RTimothyEdwards/chipalooza_projects_1/netlist/schematic/chipalooza_testchip1.spice

** sch_path: /home/tim/gits/chipalooza_projects_1/xschem/chipalooza_testchip1.sch
.subckt chipalooza_testchip1 vccd2 vdda1 vdda2 vssa1 la_data_out[37] vssa2 la_data_out[65] la_data_out[36] la_data_out[62]
+ la_data_out[64] la_data_out[63] gpio_noesd[7] io_analog[4] gpio_analog[8] la_data_out[67] la_data_out[60] la_data_out[66] la_data_out[61]
+ io_out[13] la_data_out[34] io_analog[10] la_data_out[124] gpio_analog[9] la_data_out[91] la_data_out[69] la_data_out[58] la_data_out[87]
+ la_data_out[68] la_data_out[35] gpio_analog[6] ls_data_out[59] la_data_out[88] la_data_out[89] io_analog[3] la_data_out[90] la_data_out[17]
+ io_analog[9] la_data_out[123] gpio_analog[10] la_data_out[71] la_data_out[56] gpio_analog[5] la_data_out[70] la_data_out[57] io_analog[8]
+ la_data_out[25] la_data_out[73] la_data_out[54] la_data_out[26] io_out[17] la_data_out[72] la_data_out[55] la_data_out[27] la_data_out[86]
+ la_data_out[29] la_data_out[33] io_out[12] la_data_out[30] la_data_out[28] la_data_out[32] la_data_out[85] io_analog[2] io_analog[7]
+ la_data_out[31] la_data_out[122] la_data_out[75] la_data_out[52] la_data_out[74] la_data_out[53] gpio_noesd[2] gpio_noesd[3] gpio_noesd[4]
+ la_data_out[23] io_analog[1] io_analog[6] gpio_analog[11] la_data_out[121] la_data_out[77] la_data_out[50] la_data_out[76] gpio_analog[1]
+ la_data_out[51] io_out[8] la_data_out[22] io_out[7] la_data_out[96] io_analog[0] io_out[3] io_analog[5] la_data_out[97] io_out[2] gpio_analog[13]
+ la_data_out[98] gpio_analog[12] io_out[4] la_data_out[94] la_data_out[118] la_data_out[93] la_data_in[120] la_data_out[92] la_data_out[99]
+ la_data_in[119] gpio_analog[0] la_data_out[95] la_data_out[21] io_out[6] la_data_out[105] gpio_analog[17] la_data_out[104] la_data_out[48]
+ la_data_out[103] la_data_out[41] la_data_out[102] la_data_out[44] la_data_out[100] la_data_out[40] la_data_out[101] la_data_out[42]
+ la_data_out[38] la_data_out[46] la_data_out[19] la_data_out[47] la_data_out[20] la_data_out[49] io_out[23] la_data_out[45] gpio_analog[15]
+ gpio_analog[14] la_data_out[39] la_data_out[43] la_data_out[78] la_data_out[125] io_out[0] la_data_out[84] la_data_out[82] io_out[1]
+ la_data_out[81] la_data_out[112] la_data_out[16] la_data_out[83] la_data_out[113] la_data_out[15] la_data_out[80] la_data_out[111]
+ la_data_out[14] la_data_out[79] la_data_out[13] la_data_out[107] la_data_out[109] la_data_in[117] la_data_out[12] la_data_out[106]
+ la_data_out[115] io_out[5] la_data_out[11] la_data_out[108] la_data_out[114] la_data_out[10] la_data_out[116] la_data_out[9] la_data_out[110]
+ la_data_out[8] la_data_out[7] la_data_out[6] la_data_out[5] la_data_out[4] la_data_out[3] la_data_out[2] la_data_out[1] gpio_analog[18]
+ io_oeb[0] io_oeb[17] io_oeb[1] io_oeb[23] io_oeb[2] io_oeb[3] io_oeb[4] io_oeb[5] io_oeb[6] io_oeb[7] io_oeb[8] io_oeb[12] io_oeb[13]
*.PININFO vdda1:I vssa1:I vccd2:I vdda2:I vssa2:I la_data_out[50]:I la_data_out[51]:I la_data_out[62]:I la_data_out[63]:I
*+ la_data_out[60]:I la_data_out[61]:I la_data_out[58]:I ls_data_out[59]:I la_data_out[56]:I la_data_out[57]:I la_data_out[54]:I la_data_out[55]:I
*+ la_data_out[52]:I la_data_out[53]:I la_data_out[77]:I la_data_out[76]:I la_data_out[75]:I la_data_out[74]:I la_data_out[73]:I la_data_out[72]:I
*+ la_data_out[71]:I la_data_out[70]:I la_data_out[69]:I la_data_out[68]:I la_data_out[67]:I la_data_out[66]:I la_data_out[65]:I la_data_out[64]:I
*+ gpio_analog[17]:I la_data_out[49]:I la_data_out[48]:I la_data_out[47]:I la_data_out[46]:I la_data_out[45]:I la_data_out[44]:I la_data_out[43]:I
*+ la_data_out[42]:I la_data_out[41]:I la_data_out[40]:I la_data_out[39]:I la_data_out[38]:I la_data_out[84]:I la_data_out[83]:I la_data_out[82]:I
*+ la_data_out[81]:I la_data_out[80]:I la_data_out[79]:I la_data_out[78]:I la_data_out[125]:I vssa1:I vdda1:I gpio_analog[18]:B gpio_analog[14]:B
*+ gpio_analog[15]:B la_data_out[19]:I la_data_out[20]:I io_out[23]:O la_data_out[16]:I gpio_analog[13]:B la_data_out[21]:I gpio_analog[12]:B
*+ gpio_analog[11]:B la_data_out[22]:I la_data_out[23]:I la_data_out[33]:I la_data_out[32]:I la_data_out[31]:I la_data_out[27]:I la_data_out[26]:I
*+ la_data_out[25]:I io_out[17]:O la_data_out[30]:I la_data_out[29]:I la_data_out[28]:I gpio_analog[10]:B la_data_out[17]:I la_data_out[34]:I
*+ la_data_out[36]:I gpio_analog[9]:B gpio_analog[8]:B la_data_out[35]:I la_data_out[37]:I gpio_noesd[7]:B io_out[13]:O la_data_out[91]:I
*+ la_data_out[90]:I la_data_out[89]:I la_data_out[88]:I la_data_out[87]:I gpio_analog[6]:B la_data_out[124]:I gpio_analog[5]:B la_data_out[123]:I
*+ io_out[12]:O gpio_noesd[4]:B gpio_noesd[3]:B la_data_out[85]:I la_data_out[86]:I gpio_noesd[2]:B la_data_out[122]:I gpio_analog[1]:B
*+ la_data_out[121]:I gpio_analog[0]:B la_data_out[118]:I io_out[2]:O io_out[7]:O io_out[8]:O io_out[3]:O la_data_in[119]:O la_data_out[92]:I
*+ la_data_out[93]:I la_data_out[94]:I io_out[4]:O la_data_out[98]:I la_data_out[97]:I la_data_out[96]:I la_data_out[95]:I la_data_out[99]:I
*+ la_data_in[120]:O io_out[6]:O la_data_out[105]:I la_data_out[104]:I la_data_out[103]:I la_data_out[102]:I la_data_out[101]:I la_data_out[100]:I
*+ io_out[0]:O io_out[5]:O la_data_out[107]:I la_data_out[106]:I la_data_out[108]:I la_data_in[117]:O la_data_out[116]:I io_out[1]:O
*+ la_data_out[115]:I la_data_out[114]:I la_data_out[112]:I la_data_out[113]:I la_data_out[111]:I la_data_out[110]:I la_data_out[109]:I io_oeb[0]:O
*+ io_oeb[1]:O io_oeb[2]:O io_oeb[3]:O io_oeb[4]:O io_oeb[5]:O io_oeb[6]:O io_oeb[7]:O io_oeb[8]:O io_oeb[12]:O io_oeb[13]:O io_oeb[17]:O
*+ io_oeb[23]:O io_analog[10]:B io_analog[9]:B io_analog[8]:B io_analog[7]:B io_analog[6]:B io_analog[5]:B io_analog[0]:B io_analog[1]:B
*+ io_analog[2]:B io_analog[3]:B io_analog[4]:B la_data_out[1]:I la_data_out[2]:I la_data_out[3]:I la_data_out[4]:I la_data_out[5]:I
*+ la_data_out[6]:I la_data_out[7]:I la_data_out[8]:I la_data_out[9]:I la_data_out[10]:I la_data_out[11]:I la_data_out[12]:I la_data_out[13]:I
*+ la_data_out[14]:I la_data_out[15]:I la_data_out[16]:I
x1 vdda1 gpio_analog[17] la_data_out[48] la_data_out[41] la_data_out[44] la_data_out[40] la_data_out[42] la_data_out[38]
+ la_data_out[46] la_data_out[47] la_data_out[49] la_data_out[45] la_data_out[39] la_data_out[43] src_200_0 src_10000_0 src_400 src_600 src_test1
+ src_200_1 src_100 src_10000_1 src_50 src_test0 src_200_2 la_data_out[78] la_data_out[125] la_data_out[84] la_data_out[82] la_data_out[81]
+ la_data_out[83] la_data_out[80] ibias_nc3 ibias_nc1 snk_5000_1 snk_test1 snk_3700 ibias_nc2 snk_test0 la_data_out[79] vssa1 bias_generator
x2 la_data_out[62] la_data_out[63] vssa2 vdda2 vdd_spare_3 power_stage
x3 la_data_out[60] la_data_out[61] vssa2 vdda2 io_analog[10] power_stage
x4 la_data_out[58] ls_data_out[59] vssa2 vccd2 io_analog[9] power_stage
x5 la_data_out[56] la_data_out[57] vssa2 vdda2 io_analog[8] power_stage
x6 la_data_out[54] la_data_out[55] vssa2 vdda2 io_analog[7] power_stage
x7 la_data_out[52] la_data_out[53] vssa2 vdda2 io_analog[6] power_stage
x8 la_data_out[50] la_data_out[51] vssa2 vccd2 io_analog[5] power_stage
x9 la_data_out[65] la_data_out[64] vssa1 vdda1 io_analog[4] power_stage
x10 la_data_out[67] la_data_out[66] vssa1 vdda1 vdd_spare_2 power_stage
x11 la_data_out[69] la_data_out[68] vssa1 vdda1 io_analog[3] power_stage
x12 la_data_out[71] la_data_out[70] vssa1 vdda1 vdd_spare_1 power_stage
x13 la_data_out[73] la_data_out[72] vssa1 vdda1 io_analog[2] power_stage
x14 la_data_out[75] la_data_out[74] vssa1 vdda1 io_analog[1] power_stage
x15 la_data_out[77] la_data_out[76] vssa1 vdda1 io_analog[0] power_stage
X17 net4 gpio_analog[13] src_10000_1 net20 vssa2 io_analog[7] net2 net1 net3 lpopamp
x18 io_analog[0] vssa1 io_out[0] vccd1 net21 vssd1 io_out[1] vbgA net15 net15 net15 net22 net23 net16 net16 net16 net24
+ la_data_out[109] la_data_out[115] net25 la_data_out[114] la_data_in[117] io_out[5] la_data_out[116] la_data_out[110] src_200_0
+ sky130_ajc_ip__brownout
x19 io_analog[1] vssa1 vccd1 vssd1 vbgA io_out[6] net26 net14 net14 net14 net14 net27 la_data_out[100] la_data_out[101] src_200_1
+ sky130_ajc_ip__overvoltage
x20 io_analog[2] net28 io_out[8] vssa1 vccd1 io_out[7] vssd1 io_out[3] vbgA io_out[2] net13 net13 net13 net29 la_data_out[94]
+ io_out[4] net30 la_data_out[93] la_data_out[92] la_data_in[120] la_data_in[119] la_data_out[99] la_data_out[95] src_200_2
+ sky130_ajc_ip__por
x21 vccd2 io_analog[8] vssa2 net6 io_out[17] net5 la_data_out[28] net8 net8 net7 net7 net7 net7 net7 net7 src_400
+ sky130_ak_ip__comparator
x22 io_analog[3] vssa1 vccd1 vssd1 src_50 la_data_out[86] la_data_out[85] io_out[12] gpio_noesd[3] gpio_noesd[4]
+ sky130_be_ip__lsxo
X23 gpio_analog[15] gpio_analog[14] la_data_out[19] la_data_out[20] io_out[23] io_analog[6] vccd2 vssa2 vssd2 src_10000_0 vssd2
+ sky130_ht_ip__hsxo_cpz1
x25 io_analog[10] gpio_noesd[7] src_100 net12 net11 vssa2 vccd2 vssd2 la_data_out[37] sky130_td_ip__opamp_hp
x26 io_analog[4] vccd1 la_data_out[91] la_data_out[87] src_600 la_data_out[88] io_out[13] vbgA la_data_out[89] la_data_out[90]
+ vssd1 vssa1 sky130_vbl_ip__overvoltage
x28 la_data_out[21] net1 net2 vccd2 vssd2 avdd2 lvl_shift_invert
x29 avss2 la_data_out[22] net5 avdd2 net3 gpio_analog[12] vccd2 vssd2 analog_mux_sel1v8
x30 avss2 la_data_out[23] net6 avdd2 net4 gpio_analog[11] vccd2 vssd2 analog_mux_sel1v8
x31 vccd2 vssd2 vssa2 la_data_out[17] gpio_analog[10] src_test1 avdd2 isolated_switch_ena1v8
x32 net10 io_analog[9] vssd2 vbgA la_data_out[35] net9 sky130_od_ip__tempsensor_ext_vp
x24 avss2 la_data_out[34] net11 avdd2 net9 gpio_analog[9] vccd2 vssd2 analog_mux_sel1v8
x33 avss2 la_data_out[36] net12 avdd2 net10 gpio_analog[8] vccd2 vssd2 analog_mux_sel1v8
x34 vccd1 vssd1 vssa1 la_data_out[124] gpio_analog[6] snk_test1 avdd1 isolated_switch_ena1v8
x35 vccd1 vssd1 vssa1 la_data_out[123] gpio_analog[5] snk_3700 avdd1 isolated_switch_ena1v8
x36 avss1 la_data_out[122] vbgA avdd1 vbgB gpio_noesd[2] vccd1 vssd1 analog_mux_sel1v8
x37 vccd1 vssd1 vssa1 la_data_out[121] gpio_analog[1] snk_5000_1 avdd1 isolated_switch_ena1v8
x38 vccd1 vssd1 vssa1 la_data_out[118] gpio_analog[0] snk_test0 avdd1 isolated_switch_ena1v8
x16 io_analog[5] net19 vssd2 net17 net18 net18 net18 net18 net18 net18 net18 net18 net18 net18 net18 net18 net18 net18 net18 net18
+ bandgap
x39 io_analog[5] vssd2 net31 net17 bias_basis_current
x40 vssa2 la_data_out[16] net19 avdd2 src_test0 gpio_analog[18] vccd2 vssd2 analog_mux_sel1v8
.ends

* expanding   symbol:  bias_generator.sym # of pins=41
** sym_path: /home/tim/gits/chipalooza_projects_1/xschem/bias_generator.sym
** sch_path: /home/tim/gits/chipalooza_projects_1/xschem/bias_generator.sch
.subckt bias_generator avdd ref_in enb enb_200_2 enb_400 enb_100 enb_200_1 enb_test1 enb_10000_1 enb_10000_0 enb_test0 enb_600
+ enb_50 enb_200_0 src_200_0 src_10000_0 src_400 src_600 src_test1 src_200_1 src_100 src_10000_1 src_50 src_test0 src_200_2 ena_test0
+ ena_2000 ena_test1 ena_5000_2 ena_5000_1 ena_3700 ena_5000_0 snk_5000_2 snk_2000 snk_5000_1 snk_test1 snk_3700 snk_5000_0 snk_test0 ena
+ avss
*.PININFO ref_in:I avss:B ena:I enb:I avdd:B enb_test0:I ena_test0:I src_test0:B snk_test0:B ena_test1:I snk_test1:B enb_test1:I
*+ src_test1:B enb_10000_0:I src_10000_0:B ena_5000_0:I snk_5000_0:B enb_10000_1:I src_10000_1:B ena_5000_1:I snk_5000_1:B ena_5000_2:I
*+ snk_5000_2:B enb_600:I src_600:B enb_400:I src_400:B enb_200_0:I src_200_0:B enb_200_1:I src_200_1:B enb_200_2:I src_200_2:B enb_100:I
*+ src_100:B enb_50:I src_50:B ena_3700:I snk_3700:B ena_2000:I snk_2000:B
x2[19] net1 ena nbias nbias avss bias_nstack
x2[18] net1 ena nbias nbias avss bias_nstack
x2[17] net1 ena nbias nbias avss bias_nstack
x2[16] net1 ena nbias nbias avss bias_nstack
x2[15] net1 ena nbias nbias avss bias_nstack
x2[14] net1 ena nbias nbias avss bias_nstack
x2[13] net1 ena nbias nbias avss bias_nstack
x2[12] net1 ena nbias nbias avss bias_nstack
x2[11] net1 ena nbias nbias avss bias_nstack
x2[10] net1 ena nbias nbias avss bias_nstack
x2[9] net1 ena nbias nbias avss bias_nstack
x2[8] net1 ena nbias nbias avss bias_nstack
x2[7] net1 ena nbias nbias avss bias_nstack
x2[6] net1 ena nbias nbias avss bias_nstack
x2[5] net1 ena nbias nbias avss bias_nstack
x2[4] net1 ena nbias nbias avss bias_nstack
x2[3] net1 ena nbias nbias avss bias_nstack
x2[2] net1 ena nbias nbias avss bias_nstack
x2[1] net1 ena nbias nbias avss bias_nstack
x2[0] net1 ena nbias nbias avss bias_nstack
XR3 net1 pcasc avss sky130_fd_pr__res_high_po_0p35 L=900 mult=1 m=1
XR4 pcasc ref_in avss sky130_fd_pr__res_high_po_0p35 L=1500 mult=1 m=1
x4 net2 ena net3 nbias avss bias_nstack
x2 avdd pbias pcasc pbias enb avss net2 bias_pstack
x13[1] avdd pbias pcasc net4[1] enb_test0 avss src_test0 bias_pstack
x13[0] avdd pbias pcasc net4[0] enb_test0 avss src_test0 bias_pstack
x17[1] snk_test0 ena_test0 net5[1] nbias avss bias_nstack
x17[0] snk_test0 ena_test0 net5[0] nbias avss bias_nstack
x18[1] snk_test1 ena_test1 net6[1] nbias avss bias_nstack
x18[0] snk_test1 ena_test1 net6[0] nbias avss bias_nstack
x16[1] avdd pbias pcasc net7[1] enb_test1 avss src_test1 bias_pstack
x16[0] avdd pbias pcasc net7[0] enb_test1 avss src_test1 bias_pstack
x8[199] avdd pbias pcasc net8[199] enb_10000_0 avss src_10000_0 bias_pstack
x8[198] avdd pbias pcasc net8[198] enb_10000_0 avss src_10000_0 bias_pstack
x8[197] avdd pbias pcasc net8[197] enb_10000_0 avss src_10000_0 bias_pstack
x8[196] avdd pbias pcasc net8[196] enb_10000_0 avss src_10000_0 bias_pstack
x8[195] avdd pbias pcasc net8[195] enb_10000_0 avss src_10000_0 bias_pstack
x8[194] avdd pbias pcasc net8[194] enb_10000_0 avss src_10000_0 bias_pstack
x8[193] avdd pbias pcasc net8[193] enb_10000_0 avss src_10000_0 bias_pstack
x8[192] avdd pbias pcasc net8[192] enb_10000_0 avss src_10000_0 bias_pstack
x8[191] avdd pbias pcasc net8[191] enb_10000_0 avss src_10000_0 bias_pstack
x8[190] avdd pbias pcasc net8[190] enb_10000_0 avss src_10000_0 bias_pstack
x8[189] avdd pbias pcasc net8[189] enb_10000_0 avss src_10000_0 bias_pstack
x8[188] avdd pbias pcasc net8[188] enb_10000_0 avss src_10000_0 bias_pstack
x8[187] avdd pbias pcasc net8[187] enb_10000_0 avss src_10000_0 bias_pstack
x8[186] avdd pbias pcasc net8[186] enb_10000_0 avss src_10000_0 bias_pstack
x8[185] avdd pbias pcasc net8[185] enb_10000_0 avss src_10000_0 bias_pstack
x8[184] avdd pbias pcasc net8[184] enb_10000_0 avss src_10000_0 bias_pstack
x8[183] avdd pbias pcasc net8[183] enb_10000_0 avss src_10000_0 bias_pstack
x8[182] avdd pbias pcasc net8[182] enb_10000_0 avss src_10000_0 bias_pstack
x8[181] avdd pbias pcasc net8[181] enb_10000_0 avss src_10000_0 bias_pstack
x8[180] avdd pbias pcasc net8[180] enb_10000_0 avss src_10000_0 bias_pstack
x8[179] avdd pbias pcasc net8[179] enb_10000_0 avss src_10000_0 bias_pstack
x8[178] avdd pbias pcasc net8[178] enb_10000_0 avss src_10000_0 bias_pstack
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
x8[1] avdd pbias pcasc net8[1] enb_10000_0 avss src_10000_0 bias_pstack
x8[0] avdd pbias pcasc net8[0] enb_10000_0 avss src_10000_0 bias_pstack
x9[99] snk_5000_0 ena_5000_0 net9[99] nbias avss bias_nstack
x9[98] snk_5000_0 ena_5000_0 net9[98] nbias avss bias_nstack
x9[97] snk_5000_0 ena_5000_0 net9[97] nbias avss bias_nstack
x9[96] snk_5000_0 ena_5000_0 net9[96] nbias avss bias_nstack
x9[95] snk_5000_0 ena_5000_0 net9[95] nbias avss bias_nstack
x9[94] snk_5000_0 ena_5000_0 net9[94] nbias avss bias_nstack
x9[93] snk_5000_0 ena_5000_0 net9[93] nbias avss bias_nstack
x9[92] snk_5000_0 ena_5000_0 net9[92] nbias avss bias_nstack
x9[91] snk_5000_0 ena_5000_0 net9[91] nbias avss bias_nstack
x9[90] snk_5000_0 ena_5000_0 net9[90] nbias avss bias_nstack
x9[89] snk_5000_0 ena_5000_0 net9[89] nbias avss bias_nstack
x9[88] snk_5000_0 ena_5000_0 net9[88] nbias avss bias_nstack
x9[87] snk_5000_0 ena_5000_0 net9[87] nbias avss bias_nstack
x9[86] snk_5000_0 ena_5000_0 net9[86] nbias avss bias_nstack
x9[85] snk_5000_0 ena_5000_0 net9[85] nbias avss bias_nstack
x9[84] snk_5000_0 ena_5000_0 net9[84] nbias avss bias_nstack
x9[83] snk_5000_0 ena_5000_0 net9[83] nbias avss bias_nstack
x9[82] snk_5000_0 ena_5000_0 net9[82] nbias avss bias_nstack
x9[81] snk_5000_0 ena_5000_0 net9[81] nbias avss bias_nstack
x9[80] snk_5000_0 ena_5000_0 net9[80] nbias avss bias_nstack
x9[79] snk_5000_0 ena_5000_0 net9[79] nbias avss bias_nstack
x9[78] snk_5000_0 ena_5000_0 net9[78] nbias avss bias_nstack
x9[77] snk_5000_0 ena_5000_0 net9[77] nbias avss bias_nstack
x9[76] snk_5000_0 ena_5000_0 net9[76] nbias avss bias_nstack
x9[75] snk_5000_0 ena_5000_0 net9[75] nbias avss bias_nstack
x9[74] snk_5000_0 ena_5000_0 net9[74] nbias avss bias_nstack
x9[73] snk_5000_0 ena_5000_0 net9[73] nbias avss bias_nstack
x9[72] snk_5000_0 ena_5000_0 net9[72] nbias avss bias_nstack
x9[71] snk_5000_0 ena_5000_0 net9[71] nbias avss bias_nstack
x9[70] snk_5000_0 ena_5000_0 net9[70] nbias avss bias_nstack
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
