RTimothyEdwards/chipalooza_projects_1/netlist/schematic/bias_generator.spice

** sch_path: /home/tim/gits/chipalooza_projects_1/xschem/bias_generator.sch
.subckt bias_generator avdd ref_in enb enb_200_2 enb_400 enb_100 enb_200_1 enb_test1 enb_10000_1 enb_10000_0 enb_test0 enb_600
+ enb_50 enb_200_0 src_200_0 src_10000_0 src_400 src_600 src_test1 src_200_1 src_100 src_10000_1 src_50 src_test0 src_200_2 ena_test0
+ ena_2000 ena_test1 ena_5000_2 ena_5000_1 ena_3700 ena_5000_0 snk_5000_2 snk_2000 snk_5000_1 snk_test1 snk_3700 snk_5000_0 snk_test0 ena
+ avss
*.PININFO ref_in:I avss:B ena:I enb:I avdd:B enb_test0:I ena_test0:I src_test0:B snk_test0:B ena_test1:I snk_test1:B enb_test1:I
*+ src_test1:B enb_10000_0:I src_10000_0:B ena_5000_0:I snk_5000_0:B enb_10000_1:I src_10000_1:B ena_5000_1:I snk_5000_1:B ena_5000_2:I
*+ snk_5000_2:B enb_600:I src_600:B enb_400:I src_400:B enb_200_0:I src_200_0:B enb_200_1:I src_200_1:B enb_200_2:I src_200_2:B enb_100:I
*+ src_100:B enb_50:I src_50:B ena_3700:I snk_3700:B ena_2000:I snk_2000:B
x2[19] net1 ena nbias nbias avss bias_nstack
x2[18] net1 ena nbias nbias avss bias_nstack
x2[17] net1 ena nbias nbias avss bias_nstack
x2[16] net1 ena nbias nbias avss bias_nstack
x2[15] net1 ena nbias nbias avss bias_nstack
x2[14] net1 ena nbias nbias avss bias_nstack
x2[13] net1 ena nbias nbias avss bias_nstack
x2[12] net1 ena nbias nbias avss bias_nstack
x2[11] net1 ena nbias nbias avss bias_nstack
x2[10] net1 ena nbias nbias avss bias_nstack
x2[9] net1 ena nbias nbias avss bias_nstack
x2[8] net1 ena nbias nbias avss bias_nstack
x2[7] net1 ena nbias nbias avss bias_nstack
x2[6] net1 ena nbias nbias avss bias_nstack
x2[5] net1 ena nbias nbias avss bias_nstack
x2[4] net1 ena nbias nbias avss bias_nstack
x2[3] net1 ena nbias nbias avss bias_nstack
x2[2] net1 ena nbias nbias avss bias_nstack
x2[1] net1 ena nbias nbias avss bias_nstack
x2[0] net1 ena nbias nbias avss bias_nstack
XR3 net1 pcasc avss sky130_fd_pr__res_high_po_0p35 L=900 mult=1 m=1
XR4 pcasc ref_in avss sky130_fd_pr__res_high_po_0p35 L=1500 mult=1 m=1
x4 net2 ena net3 nbias avss bias_nstack
x2 avdd pbias pcasc pbias enb avss net2 bias_pstack
x13[1] avdd pbias pcasc net4[1] enb_test0 avss src_test0 bias_pstack
x13[0] avdd pbias pcasc net4[0] enb_test0 avss src_test0 bias_pstack
x17[1] snk_test0 ena_test0 net5[1] nbias avss bias_nstack
x17[0] snk_test0 ena_test0 net5[0] nbias avss bias_nstack
x18[1] snk_test1 ena_test1 net6[1] nbias avss bias_nstack
x18[0] snk_test1 ena_test1 net6[0] nbias avss bias_nstack
x16[1] avdd pbias pcasc net7[1] enb_test1 avss src_test1 bias_pstack
x16[0] avdd pbias pcasc net7[0] enb_test1 avss src_test1 bias_pstack
x8[199] avdd pbias pcasc net8[199] enb_10000_0 avss src_10000_0 bias_pstack
x8[198] avdd pbias pcasc net8[198] enb_10000_0 avss src_10000_0 bias_pstack
x8[197] avdd pbias pcasc net8[197] enb_10000_0 avss src_10000_0 bias_pstack
x8[196] avdd pbias pcasc net8[196] enb_10000_0 avss src_10000_0 bias_pstack
x8[195] avdd pbias pcasc net8[195] enb_10000_0 avss src_10000_0 bias_pstack
x8[194] avdd pbias pcasc net8[194] enb_10000_0 avss src_10000_0 bias_pstack
x8[193] avdd pbias pcasc net8[193] enb_10000_0 avss src_10000_0 bias_pstack
x8[192] avdd pbias pcasc net8[192] enb_10000_0 avss src_10000_0 bias_pstack
x8[191] avdd pbias pcasc net8[191] enb_10000_0 avss src_10000_0 bias_pstack
x8[190] avdd pbias pcasc net8[190] enb_10000_0 avss src_10000_0 bias_pstack
x8[189] avdd pbias pcasc net8[189] enb_10000_0 avss src_10000_0 bias_pstack
x8[188] avdd pbias pcasc net8[188] enb_10000_0 avss src_10000_0 bias_pstack
x8[187] avdd pbias pcasc net8[187] enb_10000_0 avss src_10000_0 bias_pstack
x8[186] avdd pbias pcasc net8[186] enb_10000_0 avss src_10000_0 bias_pstack
x8[185] avdd pbias pcasc net8[185] enb_10000_0 avss src_10000_0 bias_pstack
x8[184] avdd pbias pcasc net8[184] enb_10000_0 avss src_10000_0 bias_pstack
x8[183] avdd pbias pcasc net8[183] enb_10000_0 avss src_10000_0 bias_pstack
x8[182] avdd pbias pcasc net8[182] enb_10000_0 avss src_10000_0 bias_pstack
x8[181] avdd pbias pcasc net8[181] enb_10000_0 avss src_10000_0 bias_pstack
x8[180] avdd pbias pcasc net8[180] enb_10000_0 avss src_10000_0 bias_pstack
x8[179] avdd pbias pcasc net8[179] enb_10000_0 avss src_10000_0 bias_pstack
x8[178] avdd pbias pcasc net8[178] enb_10000_0 avss src_10000_0 bias_pstack
x8[177] avdd pbias pcasc net8[177] enb_10000_0 avss src_10000_0 bias_pstack
x8[176] avdd pbias pcasc net8[176] enb_10000_0 avss src_10000_0 bias_pstack
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
x10[125] avdd pbias pcasc net10[125] enb_10000_1 avss src_10000_1 bias_pstack
x10[124] avdd pbias pcasc net10[124] enb_10000_1 avss src_10000_1 bias_pstack
x10[123] avdd pbias pcasc net10[123] enb_10000_1 avss src_10000_1 bias_pstack
x10[122] avdd pbias pcasc net10[122] enb_10000_1 avss src_10000_1 bias_pstack
x10[121] avdd pbias pcasc net10[121] enb_10000_1 avss src_10000_1 bias_pstack
x10[120] avdd pbias pcasc net10[120] enb_10000_1 avss src_10000_1 bias_pstack
x10[119] avdd pbias pcasc net10[119] enb_10000_1 avss src_10000_1 bias_pstack
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
