RTimothyEdwards/chipalooza_projects_1/netlist/layout/bias_generator.spice

* NGSPICE file created from bias_generator.ext - technology: sky130A

.subckt sky130_fd_pr__nfet_g5v0d10v5_C3WBNQ a_n296_n522# a_n158_n300# a_n100_n388#
+ a_100_n300#
X0 a_100_n300# a_n100_n388# a_n158_n300# a_n296_n522# sky130_fd_pr__nfet_g5v0d10v5 ad=0.87 pd=6.58 as=0.87 ps=6.58 w=3 l=1
.ends

.subckt sky130_fd_pr__diode_pw2nd_05v5_FT76RK a_n147_n147# a_n45_n45#
X0 a_n147_n147# a_n45_n45# sky130_fd_pr__diode_pw2nd_05v5 perim=1.8e+06 area=2.025e+11
.ends

.subckt sky130_fd_pr__nfet_05v0_nvt_QRKT8P a_n296_n522# a_n158_n300# a_n100_n388#
+ a_100_n300#
X0 a_100_n300# a_n100_n388# a_n158_n300# a_n296_n522# sky130_fd_pr__nfet_05v0_nvt ad=0.87 pd=6.58 as=0.87 ps=6.58 w=3 l=1
.ends

.subckt sky130_fd_pr__nfet_g5v0d10v5_ZMKT8P a_n296_n522# a_n158_n300# a_n100_n388#
+ a_100_n300#
X0 a_100_n300# a_n100_n388# a_n158_n300# a_n296_n522# sky130_fd_pr__nfet_g5v0d10v5 ad=0.87 pd=6.58 as=0.87 ps=6.58 w=3 l=1
.ends

.subckt bias_nstack itail ena nbias avss vcasc
XXM12 avss avss nbias m1_3726_n2502# sky130_fd_pr__nfet_g5v0d10v5_C3WBNQ
Xsky130_fd_pr__diode_pw2nd_05v5_FT76RK_0 avss ena sky130_fd_pr__diode_pw2nd_05v5_FT76RK
XXM6 avss vcasc nbias m1_3726_n2502# sky130_fd_pr__nfet_05v0_nvt_QRKT8P
XXM7 avss vcasc ena itail sky130_fd_pr__nfet_g5v0d10v5_ZMKT8P
.ends

.subckt sky130_fd_pr__res_high_po_0p35_P35QVK a_380_2984# a_5692_n3416# a_n3770_2984#
+ a_3866_2984# a_3202_n3416# a_n1446_n3416# a_n284_n3416# a_n616_2984# a_4696_n3416#
+ a_4198_2984# a_2206_n3416# a_n1114_2984# a_n4102_2984# a_n616_n3416# a_6190_n3416#
+ a_n6592_2984# a_2372_2984# a_n5762_n3416# a_5360_2984# a_214_2984# a_n3604_2984#
+ a_1210_n3416# a_5194_n3416# a_6522_n3416# a_n4766_n3416# a_1874_2984# a_4862_2984#
+ a_4198_n3416# a_5526_n3416# a_5194_2984# a_n6260_n3416# a_878_n3416# a_n3438_2984#
+ a_n2110_2984# a_n6426_2984# a_2206_2984# a_n118_n3416# a_n3770_n3416# a_4696_2984#
+ a_n5264_n3416# a_48_2984# a_4530_n3416# a_n2774_n3416# a_n1612_2984# a_n4600_2984#
+ a_n5928_2984# a_1708_2984# a_6024_n3416# a_n4268_n3416# a_2870_2984# a_3534_n3416#
+ a_712_2984# a_n1778_n3416# a_5028_2984# a_5028_n3416# a_n948_2984# a_2538_n3416#
+ a_6190_2984# a_n1446_2984# a_n3272_n3416# a_n4434_2984# a_n4600_n3416# a_3202_2984#
+ a_n948_n3416# a_5692_2984# a_380_n3416# a_546_2984# a_4032_n3416# a_n2276_n3416#
+ a_n3604_n3416# a_n3936_2984# a_1542_n3416# a_2704_2984# a_3036_n3416# a_712_n3416#
+ a_n2608_n3416# a_n4268_2984# a_3036_2984# a_6024_2984# a_5858_n3416# a_n1280_n3416#
+ a_n6592_n3416# a_n2442_2984# a_n4102_n3416# a_2538_2984# a_n5430_2984# a_2040_n3416#
+ a_5526_2984# a_1210_2984# a_n1612_n3416# a_n5596_n3416# a_4862_n3416# a_n450_n3416#
+ a_n1944_2984# a_n3106_n3416# a_n4932_2984# a_1044_n3416# a_n450_2984# a_3700_2984#
+ a_6356_n3416# a_214_n3416# a_n5928_n3416# a_n6722_n3546# a_3866_n3416# a_n2276_2984#
+ a_n5264_2984# a_1044_2984# a_4032_2984# a_n2110_n3416# a_n6094_n3416# a_n1778_2984#
+ a_n4766_2984# a_5360_n3416# a_n284_2984# a_3534_2984# a_n4932_n3416# a_6522_2984#
+ a_n1114_n3416# a_2870_n3416# a_n5098_n3416# a_n6426_n3416# a_878_2984# a_4364_n3416#
+ a_n5098_2984# a_n3936_n3416# a_n2940_2984# a_1874_n3416# a_3368_n3416# a_n3272_2984#
+ a_3368_2984# a_48_n3416# a_n6260_2984# a_2040_2984# a_6356_2984# a_n5430_n3416#
+ a_n2940_n3416# a_n118_2984# a_n2774_2984# a_n4434_n3416# a_n5762_2984# a_1542_2984#
+ a_2372_n3416# a_4530_2984# a_5858_2984# a_3700_n3416# a_n1944_n3416# a_n3438_n3416#
+ a_n6094_2984# a_n782_n3416# a_1376_n3416# a_n782_2984# a_2704_n3416# a_546_n3416#
+ a_n3106_2984# a_n1280_2984# a_n5596_2984# a_1376_2984# a_1708_n3416# a_4364_2984#
+ a_n2442_n3416# a_n2608_2984#
X0 a_n3936_2984# a_n3936_n3416# a_n6722_n3546# sky130_fd_pr__res_high_po_0p35 l=30
X1 a_n1612_2984# a_n1612_n3416# a_n6722_n3546# sky130_fd_pr__res_high_po_0p35 l=30
X2 a_n6592_2984# a_n6592_n3416# a_n6722_n3546# sky130_fd_pr__res_high_po_0p35 l=30
X3 a_n4434_2984# a_n4434_n3416# a_n6722_n3546# sky130_fd_pr__res_high_po_0p35 l=30
X4 a_48_2984# a_48_n3416# a_n6722_n3546# sky130_fd_pr__res_high_po_0p35 l=30
X5 a_2704_2984# a_2704_n3416# a_n6722_n3546# sky130_fd_pr__res_high_po_0p35 l=30
X6 a_4862_2984# a_4862_n3416# a_n6722_n3546# sky130_fd_pr__res_high_po_0p35 l=30
X7 a_3202_2984# a_3202_n3416# a_n6722_n3546# sky130_fd_pr__res_high_po_0p35 l=30
X8 a_5360_2984# a_5360_n3416# a_n6722_n3546# sky130_fd_pr__res_high_po_0p35 l=30
X9 a_5526_2984# a_5526_n3416# a_n6722_n3546# sky130_fd_pr__res_high_po_0p35 l=30
X10 a_n948_2984# a_n948_n3416# a_n6722_n3546# sky130_fd_pr__res_high_po_0p35 l=30
X11 a_n782_2984# a_n782_n3416# a_n6722_n3546# sky130_fd_pr__res_high_po_0p35 l=30
X12 a_6024_2984# a_6024_n3416# a_n6722_n3546# sky130_fd_pr__res_high_po_0p35 l=30
X13 a_n4932_2984# a_n4932_n3416# a_n6722_n3546# sky130_fd_pr__res_high_po_0p35 l=30
X14 a_1376_2984# a_1376_n3416# a_n6722_n3546# sky130_fd_pr__res_high_po_0p35 l=30
X15 a_878_2984# a_878_n3416# a_n6722_n3546# sky130_fd_pr__res_high_po_0p35 l=30
X16 a_4198_2984# a_4198_n3416# a_n6722_n3546# sky130_fd_pr__res_high_po_0p35 l=30
X17 a_n3770_2984# a_n3770_n3416# a_n6722_n3546# sky130_fd_pr__res_high_po_0p35 l=30
X18 a_n1446_2984# a_n1446_n3416# a_n6722_n3546# sky130_fd_pr__res_high_po_0p35 l=30
X19 a_3700_2984# a_3700_n3416# a_n6722_n3546# sky130_fd_pr__res_high_po_0p35 l=30
X20 a_n4268_2984# a_n4268_n3416# a_n6722_n3546# sky130_fd_pr__res_high_po_0p35 l=30
X21 a_n2110_2984# a_n2110_n3416# a_n6722_n3546# sky130_fd_pr__res_high_po_0p35 l=30
X22 a_1874_2984# a_1874_n3416# a_n6722_n3546# sky130_fd_pr__res_high_po_0p35 l=30
X23 a_6522_2984# a_6522_n3416# a_n6722_n3546# sky130_fd_pr__res_high_po_0p35 l=30
X24 a_2372_2984# a_2372_n3416# a_n6722_n3546# sky130_fd_pr__res_high_po_0p35 l=30
X25 a_2538_2984# a_2538_n3416# a_n6722_n3546# sky130_fd_pr__res_high_po_0p35 l=30
X26 a_4696_2984# a_4696_n3416# a_n6722_n3546# sky130_fd_pr__res_high_po_0p35 l=30
X27 a_3036_2984# a_3036_n3416# a_n6722_n3546# sky130_fd_pr__res_high_po_0p35 l=30
X28 a_5194_2984# a_5194_n3416# a_n6722_n3546# sky130_fd_pr__res_high_po_0p35 l=30
X29 a_n1944_2984# a_n1944_n3416# a_n6722_n3546# sky130_fd_pr__res_high_po_0p35 l=30
X30 a_n4766_2984# a_n4766_n3416# a_n6722_n3546# sky130_fd_pr__res_high_po_0p35 l=30
X31 a_n2608_2984# a_n2608_n3416# a_n6722_n3546# sky130_fd_pr__res_high_po_0p35 l=30
X32 a_n2442_2984# a_n2442_n3416# a_n6722_n3546# sky130_fd_pr__res_high_po_0p35 l=30
X33 a_214_2984# a_214_n3416# a_n6722_n3546# sky130_fd_pr__res_high_po_0p35 l=30
X34 a_n5430_2984# a_n5430_n3416# a_n6722_n3546# sky130_fd_pr__res_high_po_0p35 l=30
X35 a_n5264_2984# a_n5264_n3416# a_n6722_n3546# sky130_fd_pr__res_high_po_0p35 l=30
X36 a_n3106_2984# a_n3106_n3416# a_n6722_n3546# sky130_fd_pr__res_high_po_0p35 l=30
X37 a_2870_2984# a_2870_n3416# a_n6722_n3546# sky130_fd_pr__res_high_po_0p35 l=30
X38 a_n1280_2984# a_n1280_n3416# a_n6722_n3546# sky130_fd_pr__res_high_po_0p35 l=30
X39 a_1210_2984# a_1210_n3416# a_n6722_n3546# sky130_fd_pr__res_high_po_0p35 l=30
X40 a_3534_2984# a_3534_n3416# a_n6722_n3546# sky130_fd_pr__res_high_po_0p35 l=30
X41 a_5692_2984# a_5692_n3416# a_n6722_n3546# sky130_fd_pr__res_high_po_0p35 l=30
X42 a_5858_2984# a_5858_n3416# a_n6722_n3546# sky130_fd_pr__res_high_po_0p35 l=30
X43 a_712_2984# a_712_n3416# a_n6722_n3546# sky130_fd_pr__res_high_po_0p35 l=30
X44 a_4032_2984# a_4032_n3416# a_n6722_n3546# sky130_fd_pr__res_high_po_0p35 l=30
X45 a_6190_2984# a_6190_n3416# a_n6722_n3546# sky130_fd_pr__res_high_po_0p35 l=30
X46 a_6356_2984# a_6356_n3416# a_n6722_n3546# sky130_fd_pr__res_high_po_0p35 l=30
X47 a_n5928_2984# a_n5928_n3416# a_n6722_n3546# sky130_fd_pr__res_high_po_0p35 l=30
X48 a_n5762_2984# a_n5762_n3416# a_n6722_n3546# sky130_fd_pr__res_high_po_0p35 l=30
X49 a_n3604_2984# a_n3604_n3416# a_n6722_n3546# sky130_fd_pr__res_high_po_0p35 l=30
X50 a_n118_2984# a_n118_n3416# a_n6722_n3546# sky130_fd_pr__res_high_po_0p35 l=30
X51 a_n6426_2984# a_n6426_n3416# a_n6722_n3546# sky130_fd_pr__res_high_po_0p35 l=30
X52 a_n4102_2984# a_n4102_n3416# a_n6722_n3546# sky130_fd_pr__res_high_po_0p35 l=30
X53 a_n1778_2984# a_n1778_n3416# a_n6722_n3546# sky130_fd_pr__res_high_po_0p35 l=30
X54 a_4530_2984# a_4530_n3416# a_n6722_n3546# sky130_fd_pr__res_high_po_0p35 l=30
X55 a_n4600_2984# a_n4600_n3416# a_n6722_n3546# sky130_fd_pr__res_high_po_0p35 l=30
X56 a_n2276_2984# a_n2276_n3416# a_n6722_n3546# sky130_fd_pr__res_high_po_0p35 l=30
X57 a_n5098_2984# a_n5098_n3416# a_n6722_n3546# sky130_fd_pr__res_high_po_0p35 l=30
X58 a_n616_2984# a_n616_n3416# a_n6722_n3546# sky130_fd_pr__res_high_po_0p35 l=30
X59 a_1044_2984# a_1044_n3416# a_n6722_n3546# sky130_fd_pr__res_high_po_0p35 l=30
X60 a_3368_2984# a_3368_n3416# a_n6722_n3546# sky130_fd_pr__res_high_po_0p35 l=30
X61 a_546_2984# a_546_n3416# a_n6722_n3546# sky130_fd_pr__res_high_po_0p35 l=30
X62 a_n2940_2984# a_n2940_n3416# a_n6722_n3546# sky130_fd_pr__res_high_po_0p35 l=30
X63 a_n2774_2984# a_n2774_n3416# a_n6722_n3546# sky130_fd_pr__res_high_po_0p35 l=30
X64 a_380_2984# a_380_n3416# a_n6722_n3546# sky130_fd_pr__res_high_po_0p35 l=30
X65 a_n5596_2984# a_n5596_n3416# a_n6722_n3546# sky130_fd_pr__res_high_po_0p35 l=30
X66 a_n3438_2984# a_n3438_n3416# a_n6722_n3546# sky130_fd_pr__res_high_po_0p35 l=30
X67 a_n3272_2984# a_n3272_n3416# a_n6722_n3546# sky130_fd_pr__res_high_po_0p35 l=30
X68 a_n1114_2984# a_n1114_n3416# a_n6722_n3546# sky130_fd_pr__res_high_po_0p35 l=30
X69 a_n6260_2984# a_n6260_n3416# a_n6722_n3546# sky130_fd_pr__res_high_po_0p35 l=30
X70 a_n6094_2984# a_n6094_n3416# a_n6722_n3546# sky130_fd_pr__res_high_po_0p35 l=30
X71 a_1708_2984# a_1708_n3416# a_n6722_n3546# sky130_fd_pr__res_high_po_0p35 l=30
X72 a_1542_2984# a_1542_n3416# a_n6722_n3546# sky130_fd_pr__res_high_po_0p35 l=30
X73 a_2206_2984# a_2206_n3416# a_n6722_n3546# sky130_fd_pr__res_high_po_0p35 l=30
X74 a_3866_2984# a_3866_n3416# a_n6722_n3546# sky130_fd_pr__res_high_po_0p35 l=30
X75 a_2040_2984# a_2040_n3416# a_n6722_n3546# sky130_fd_pr__res_high_po_0p35 l=30
X76 a_4364_2984# a_4364_n3416# a_n6722_n3546# sky130_fd_pr__res_high_po_0p35 l=30
X77 a_5028_2984# a_5028_n3416# a_n6722_n3546# sky130_fd_pr__res_high_po_0p35 l=30
X78 a_n450_2984# a_n450_n3416# a_n6722_n3546# sky130_fd_pr__res_high_po_0p35 l=30
X79 a_n284_2984# a_n284_n3416# a_n6722_n3546# sky130_fd_pr__res_high_po_0p35 l=30
.ends

.subckt sky130_fd_pr__pfet_g5v0d10v5_G8LMTZ a_n158_n300# w_n362_n597# a_n100_n397#
+ a_100_n300#
X0 a_100_n300# a_n100_n397# a_n158_n300# w_n362_n597# sky130_fd_pr__pfet_g5v0d10v5 ad=0.87 pd=6.58 as=0.87 ps=6.58 w=3 l=1
.ends

.subckt sky130_fd_pr__pfet_g5v0d10v5_H75TTW a_n158_n300# w_n362_n597# a_n100_n397#
+ a_100_n300#
X0 a_100_n300# a_n100_n397# a_n158_n300# w_n362_n597# sky130_fd_pr__pfet_g5v0d10v5 ad=0.87 pd=6.58 as=0.87 ps=6.58 w=3 l=1
.ends

.subckt bias_pstack avdd pcasc enb itail vcasc pbias avss
XXM13 m1_2150_n1558# avdd pcasc vcasc sky130_fd_pr__pfet_g5v0d10v5_G8LMTZ
Xsky130_fd_pr__pfet_g5v0d10v5_G8LMTZ_0 itail avdd enb vcasc sky130_fd_pr__pfet_g5v0d10v5_G8LMTZ
Xsky130_fd_pr__diode_pw2nd_05v5_FT76RK_0 avss enb sky130_fd_pr__diode_pw2nd_05v5_FT76RK
Xsky130_fd_pr__pfet_g5v0d10v5_H75TTW_0 m1_2150_n1558# avdd pbias avdd sky130_fd_pr__pfet_g5v0d10v5_H75TTW
.ends

.subckt bias_generator ref_in enb ena avss enb_10000_0 src_10000_0 src_10000_1 enb_10000_1
+ enb_600 src_600 enb_400 src_400 enb_200_0 src_200_0 enb_200_1 src_200_1 enb_200_2
+ src_200_2 enb_100 src_100 enb_50 src_50 ena_5000_0 snk_2000 ena_5000_1 snk_5000_1
+ ena_5000_2 snk_5000_2 snk_3700 ena_3700 ena_test0 snk_test0 snk_test1 ena_test1
+ src_test1 enb_test1 src_test0 enb_test0 avdd snk_5000_0 ena_2000
Xbias_nstack_0[0] snk_test0 ena_test0 bias_nstack_0[9]/nbias avss bias_nstack_0[0]/vcasc
+ bias_nstack
Xbias_nstack_0[1] snk_test0 ena_test0 bias_nstack_0[9]/nbias avss bias_nstack_0[1]/vcasc
+ bias_nstack
Xbias_nstack_0[2] snk_2000 ena_2000 bias_nstack_0[9]/nbias avss bias_nstack_0[2]/vcasc
+ bias_nstack
Xbias_nstack_0[3] snk_2000 ena_2000 bias_nstack_0[9]/nbias avss bias_nstack_0[3]/vcasc
+ bias_nstack
Xbias_nstack_0[4] snk_2000 ena_2000 bias_nstack_0[9]/nbias avss bias_nstack_0[4]/vcasc
+ bias_nstack
Xbias_nstack_0[5] snk_2000 ena_2000 bias_nstack_0[9]/nbias avss bias_nstack_0[5]/vcasc
+ bias_nstack
Xbias_nstack_0[6] snk_2000 ena_2000 bias_nstack_0[9]/nbias avss bias_nstack_0[6]/vcasc
+ bias_nstack
Xbias_nstack_0[7] snk_2000 ena_2000 bias_nstack_0[9]/nbias avss bias_nstack_0[7]/vcasc
+ bias_nstack
Xbias_nstack_0[8] snk_2000 ena_2000 bias_nstack_0[9]/nbias avss bias_nstack_0[8]/vcasc
+ bias_nstack
Xbias_nstack_0[9] snk_2000 ena_2000 bias_nstack_0[9]/nbias avss bias_nstack_0[9]/vcasc
+ bias_nstack
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
+ bias_nstack
Xbias_nstack_0[160] snk_5000_0 ena_5000_0 bias_nstack_0[9]/nbias avss bias_nstack_0[160]/vcasc
+ bias_nstack
Xbias_nstack_0[161] snk_5000_0 ena_5000_0 bias_nstack_0[9]/nbias avss bias_nstack_0[161]/vcasc
+ bias_nstack
Xbias_nstack_0[162] snk_5000_0 ena_5000_0 bias_nstack_0[9]/nbias avss bias_nstack_0[162]/vcasc
+ bias_nstack
Xbias_nstack_0[163] snk_5000_1 ena_5000_1 bias_nstack_0[9]/nbias avss bias_nstack_0[163]/vcasc
+ bias_nstack
Xbias_nstack_0[164] snk_5000_1 ena_5000_1 bias_nstack_0[9]/nbias avss bias_nstack_0[164]/vcasc
+ bias_nstack
Xbias_nstack_0[165] snk_5000_1 ena_5000_1 bias_nstack_0[9]/nbias avss bias_nstack_0[165]/vcasc
+ bias_nstack
Xbias_nstack_0[166] snk_5000_1 ena_5000_1 bias_nstack_0[9]/nbias avss bias_nstack_0[166]/vcasc
+ bias_nstack
Xbias_nstack_0[167] snk_5000_1 ena_5000_1 bias_nstack_0[9]/nbias avss bias_nstack_0[167]/vcasc
+ bias_nstack
Xbias_nstack_0[168] snk_5000_1 ena_5000_1 bias_nstack_0[9]/nbias avss bias_nstack_0[168]/vcasc
+ bias_nstack
Xbias_nstack_0[169] snk_5000_1 ena_5000_1 bias_nstack_0[9]/nbias avss bias_nstack_0[169]/vcasc
+ bias_nstack
Xbias_nstack_0[170] snk_5000_1 ena_5000_1 bias_nstack_0[9]/nbias avss bias_nstack_0[170]/vcasc
+ bias_nstack
Xbias_nstack_0[171] snk_5000_1 ena_5000_1 bias_nstack_0[9]/nbias avss bias_nstack_0[171]/vcasc
+ bias_nstack
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
